nidaMert/pmod_esp32/Images/PCB_back_component_compatibility.JPG

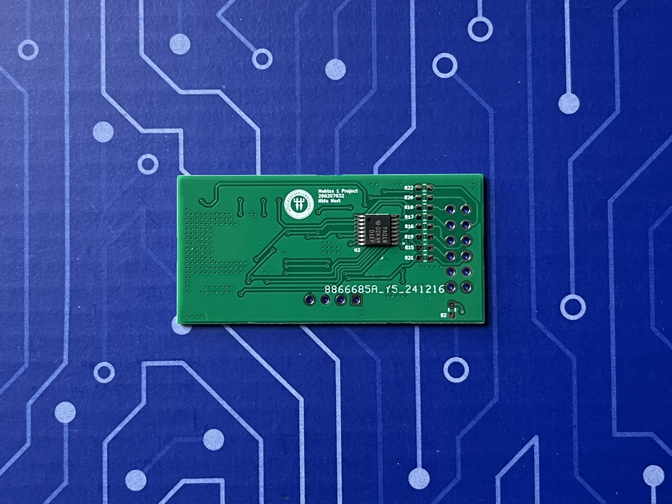
Images/PCB_back_component_compatibility.JPG
