nidaMert/pmod_esp32/Images/PCB_front_component_compatibility.JPG

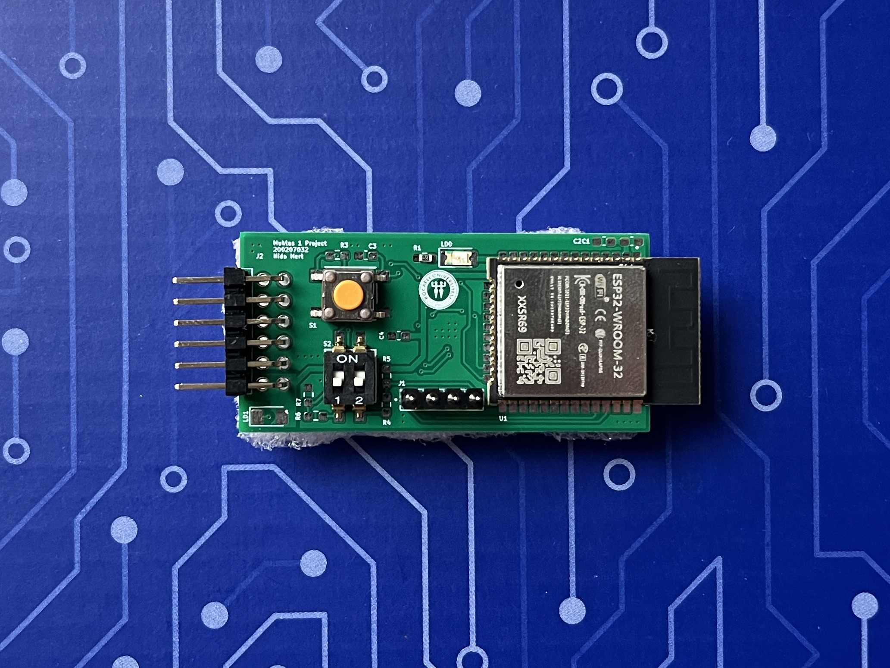
Images/PCB_front_component_compatibility.JPG
