nidaMert/pmod_esp32/Images/3_3V_ile_ilk_calistirma.JPEG

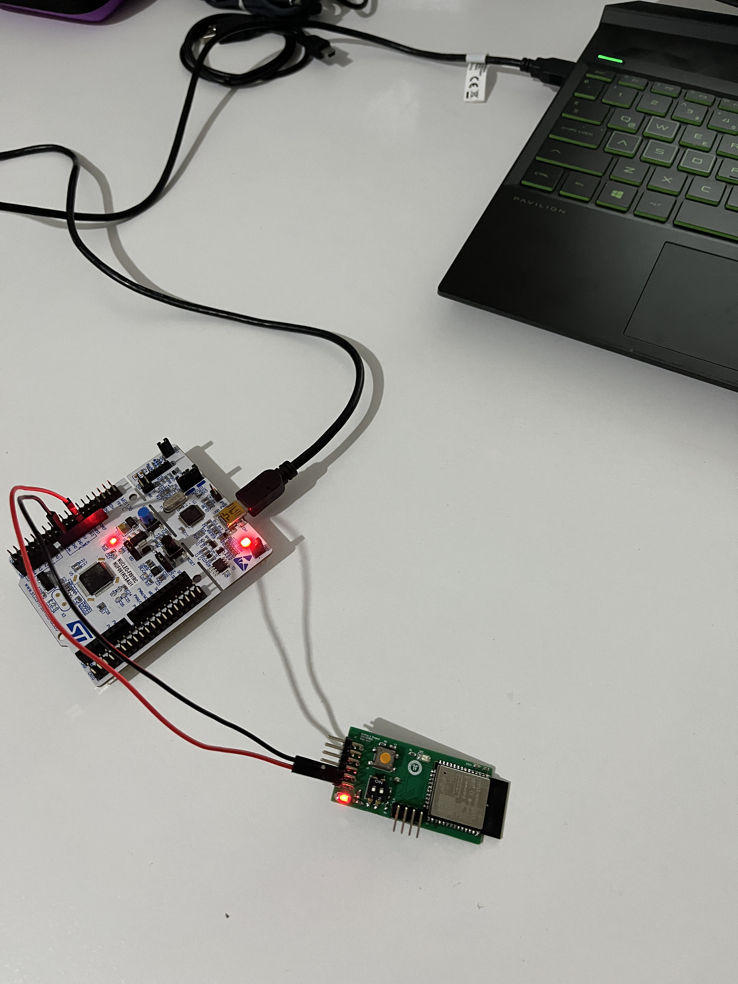
Images/3_3V_ile_ilk_calistirma.JPEG
