nidaMert/pmod_esp32/Images/Setup_for_Hercules_Utility.JPG

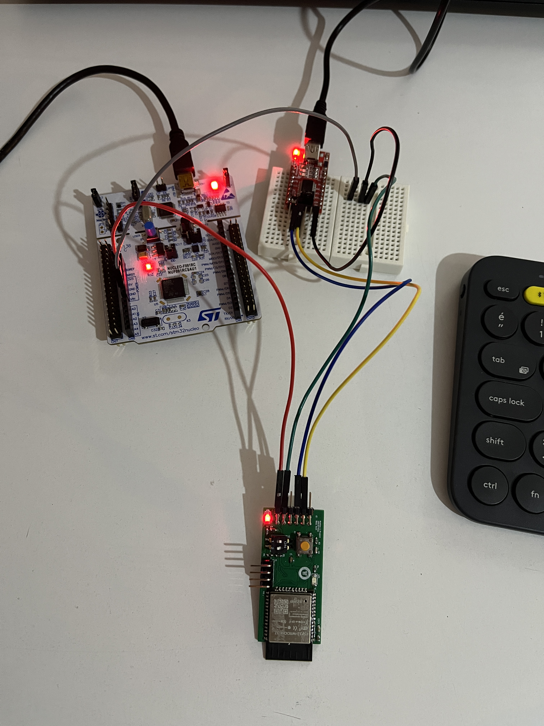
Images/Setup_for_Hercules_Utility.JPG
