nidaMert/pmod_esp32/Images/Setup_for_Test_Plan.JPG

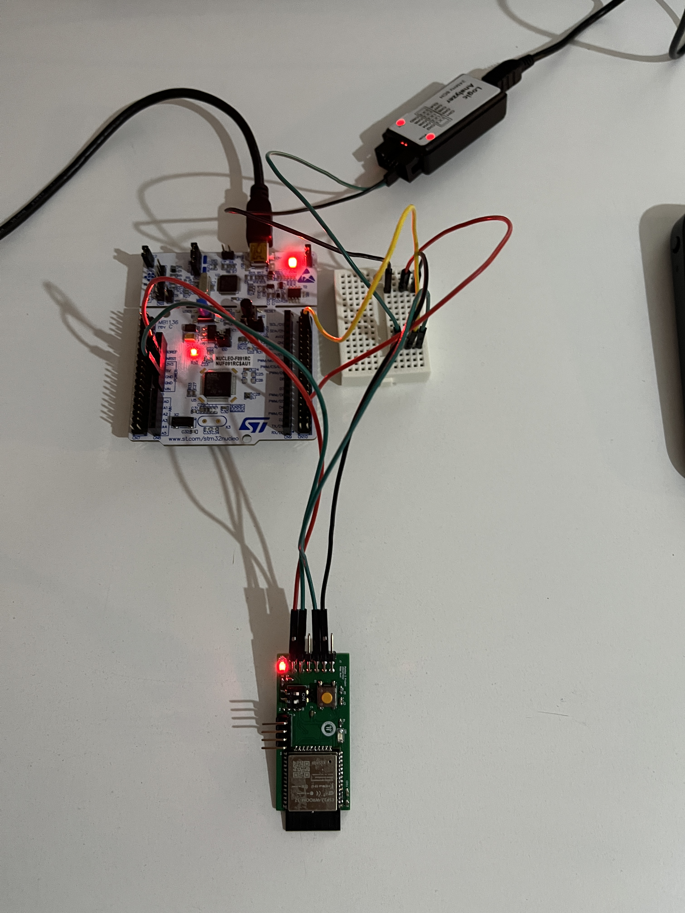
Images/Setup_for_Test_Plan.JPG
